fzxhub/esp32_pico/image/1.jpg

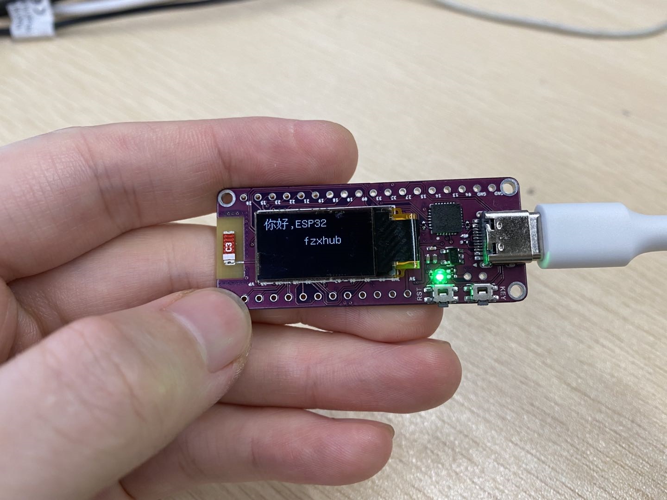
image/1.jpg
